renat2985/protimer.club/doc/AP2.png

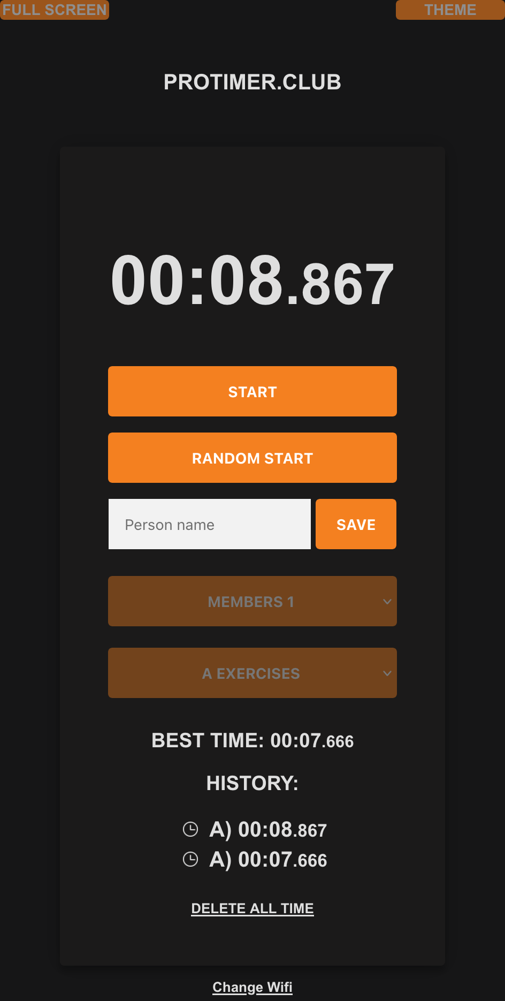
doc/AP2.png
