renat2985/protimer.club/doc/AP.png

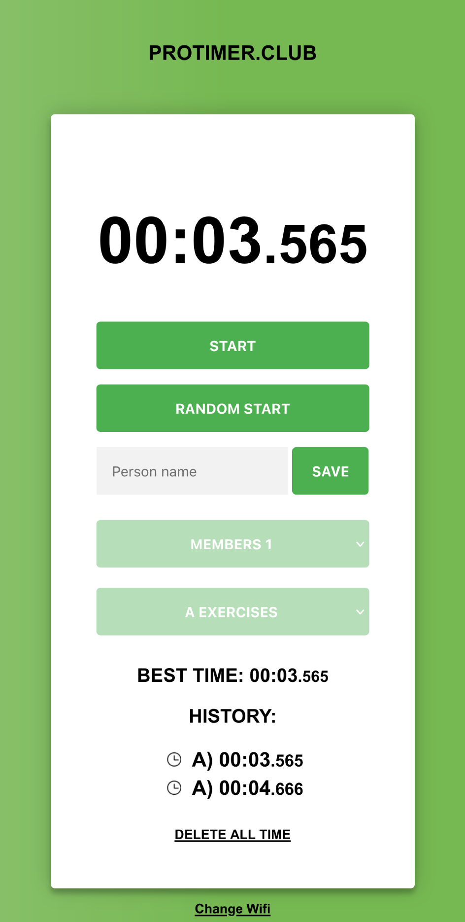
doc/AP.png
