renat2985/protimer.club/doc/protimer.png

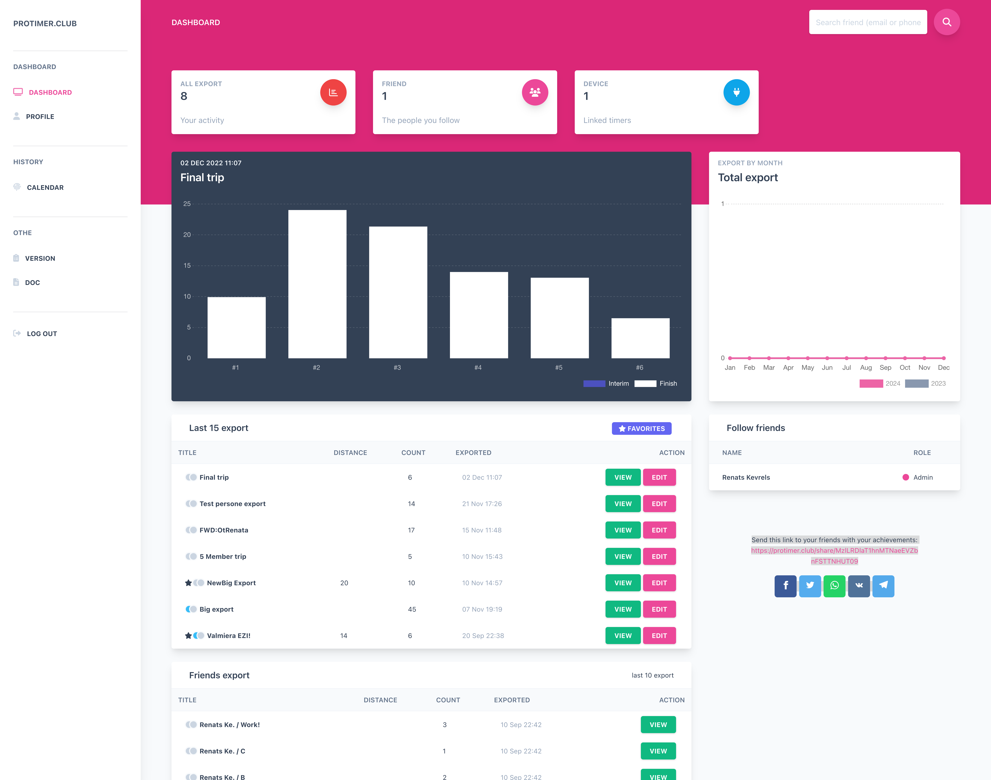
doc/protimer.png
