renat2985/protimer.club/stl/mirror4.FCStd

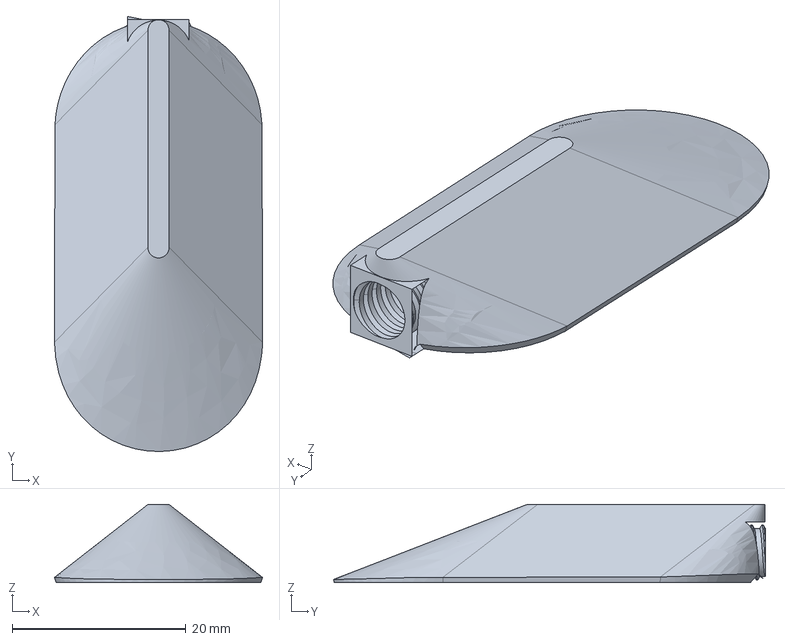
[picture p38: CAD file, 2025-02-11]
stl/mirror4.FCStd
24.0 x 50.1 x 9.00 mm
