renat2985/protimer.club/stl/mirror5.FCStd

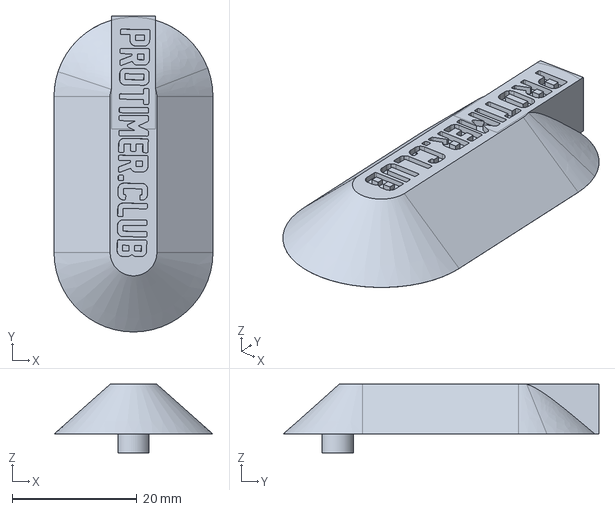
[picture p39: CAD file, 2025-02-11]
stl/mirror5.FCStd
25.5 x 50.7 x 11.0 mm
