renat2985/protimer.club/stl/mirror3.FCStd

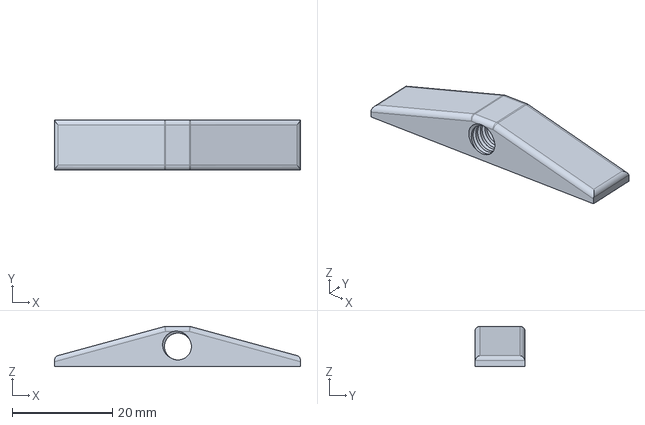
[picture p40: CAD file, 2025-02-11]
stl/mirror3.FCStd
49.0 x 10.0 x 8.00 mm
