renat2985/protimer.club/stl/othe/box-big-wemos(no hole  buzzer).step

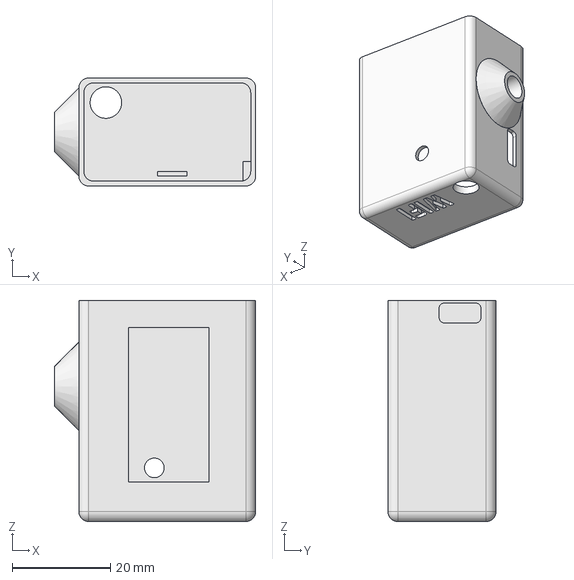
[picture p41: CAD file, 2025-02-09]
stl/othe/box-big-wemos(no hole buzzer).step
41.0 x 22.0 x 45.0 mm
