renat2985/protimer.club/stl/othe/display-clips.FCStd

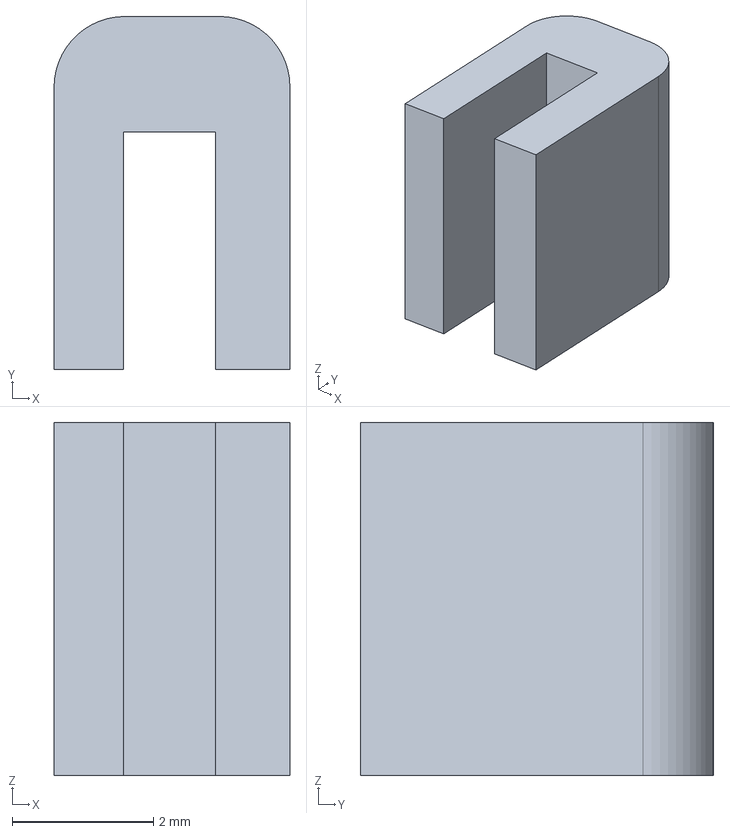
[picture p42: CAD file, 2025-01-18]
stl/othe/display-clips.FCStd
3.34 x 5.00 x 5.00 mm
