renat2985/protimer.club/stl/othe/сover-laser-microUSB.FCStd

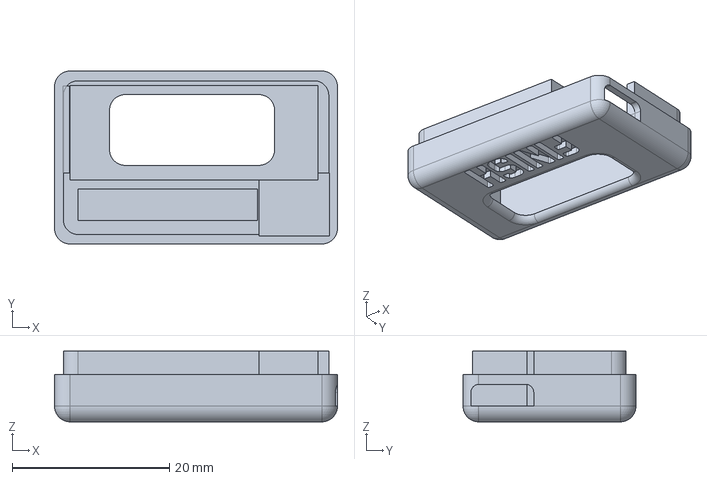
[picture p43: CAD file, 2025-01-15]
stl/othe/сover-laser-microUSB.FCStd
36.0 x 22.0 x 9.00 mm
