renat2985/protimer.club/stl/othe/сover.FCStd

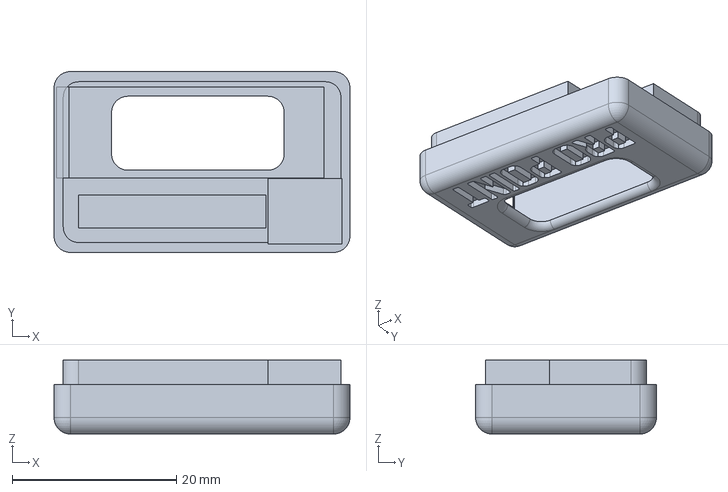
[picture p44: CAD file, 2025-01-15]
stl/othe/сover.FCStd
36.0 x 22.0 x 9.00 mm
