renat2985/protimer.club/stl/othe/box-small.FCStd

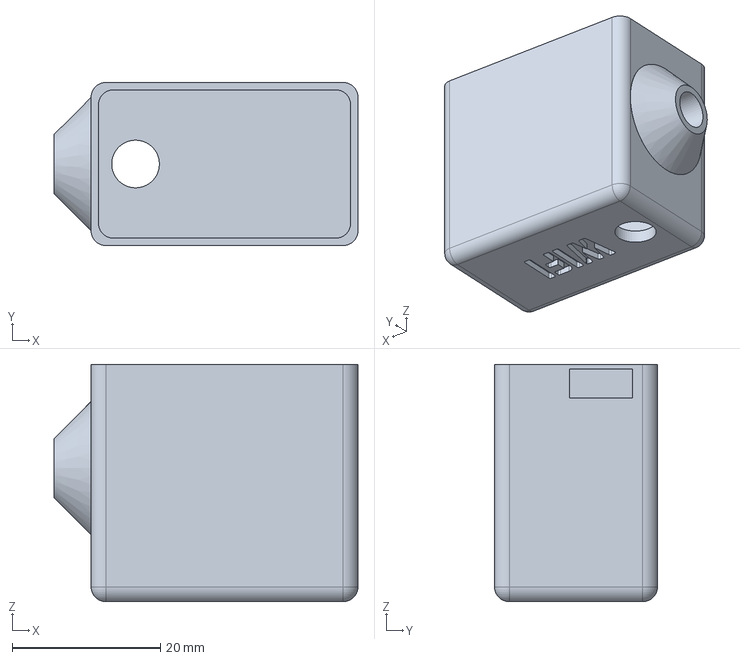
[picture p45: CAD file, 2025-01-01]
stl/othe/box-small.FCStd
41.0 x 22.0 x 32.0 mm
