renat2985/protimer.club/stl/othe/plug.FCStd

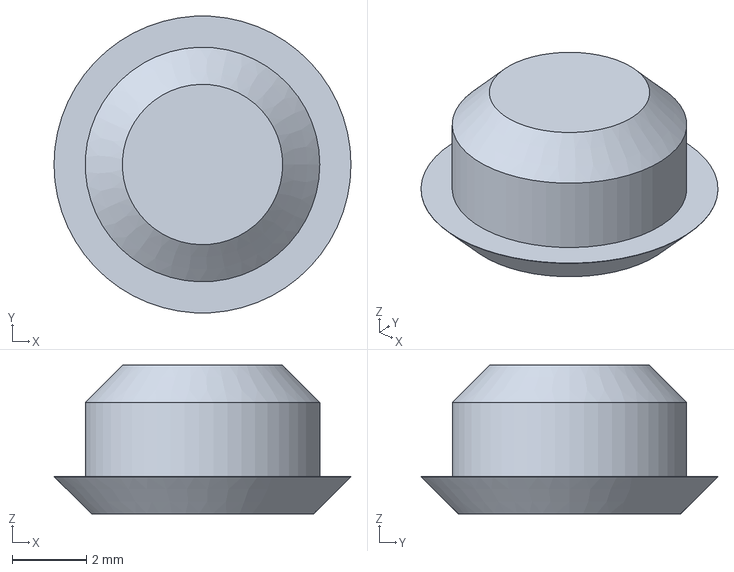
[picture p46: CAD file, 2025-01-01]
stl/othe/plug.FCStd
8.00 x 7.99 x 4.00 mm
